Tek-User/Tektronix-GPIB-Download/IMG_3034.JPG

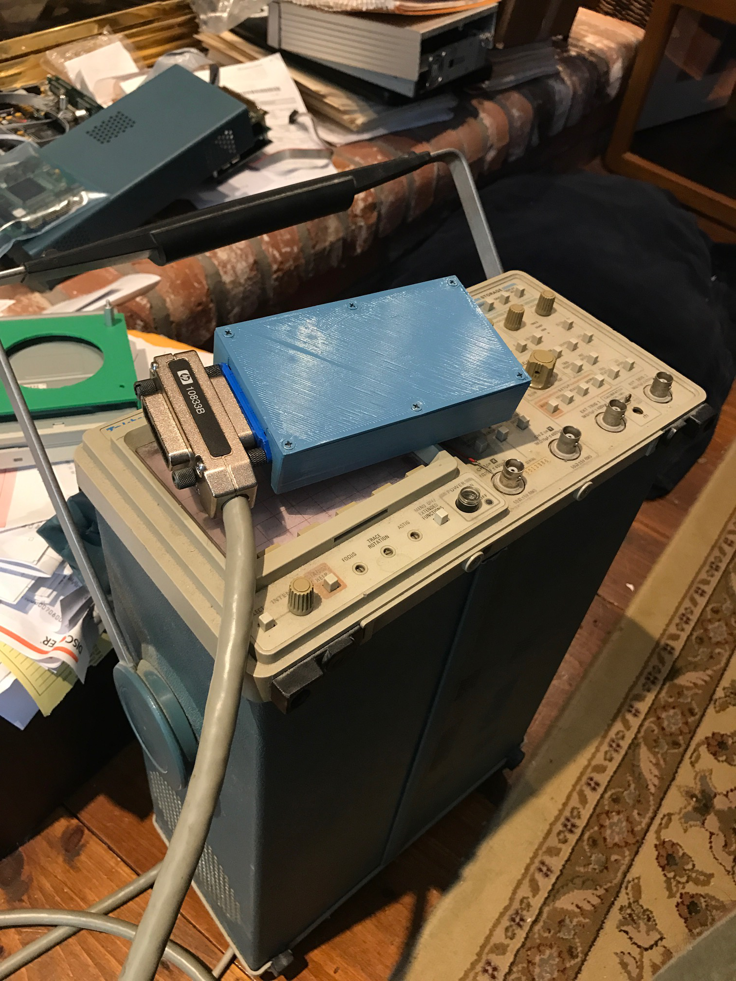
IMG_3034.JPG
