Tek-User/Tektronix-GPIB-Download/IMG_3035.JPG

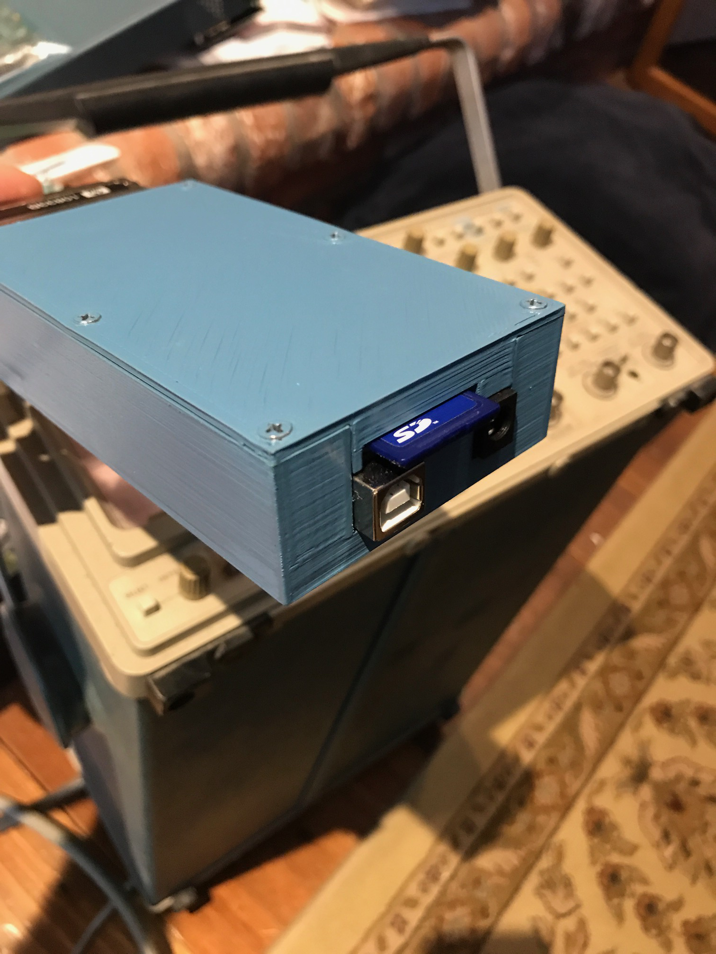
IMG_3035.JPG
