Tek-User/Tektronix-GPIB-Download/SVG.h

#ifndef SVG_h
#define SVG_h

void processSVG(void);
void print_channels(void);
void displayCurve(uint8_t textline);
void displayText(uint8_t textline);
void startSVG(void);
void endSVG(void);
void print_graticule(void);
uint8_t SD_Setup (void);

#endif
